pattarong-RAE/Cheetah_Cube_Inspire/Model/bio/oox foot.SLDPRT

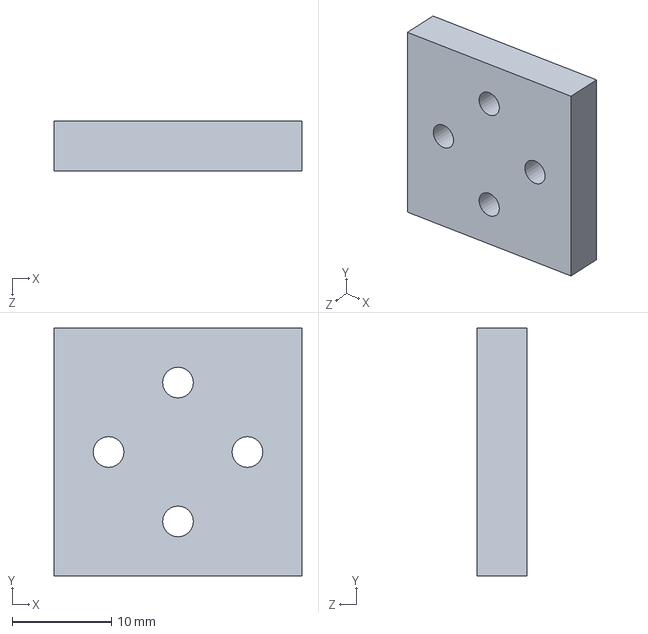
[picture p48: CAD file, 2023-05-24]
Model/bio/oox foot.SLDPRT
25.0 x 25.0 x 5.00 mm
