pattarong-RAE/Cheetah_Cube_Inspire/Model/bio/foot and body/footRingPlate.SLDPRT

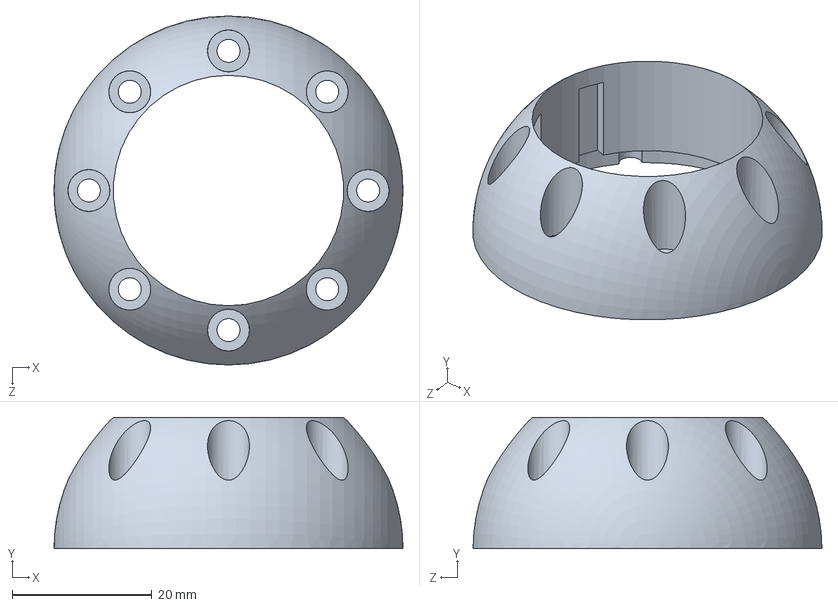
[picture p49: CAD file, 2023-05-24]
Model/bio/foot and body/footRingPlate.SLDPRT
50.0 x 18.8 x 50.0 mm
