pattarong-RAE/Cheetah_Cube_Inspire/Model/bio/sevo smail 2.SLDPRT

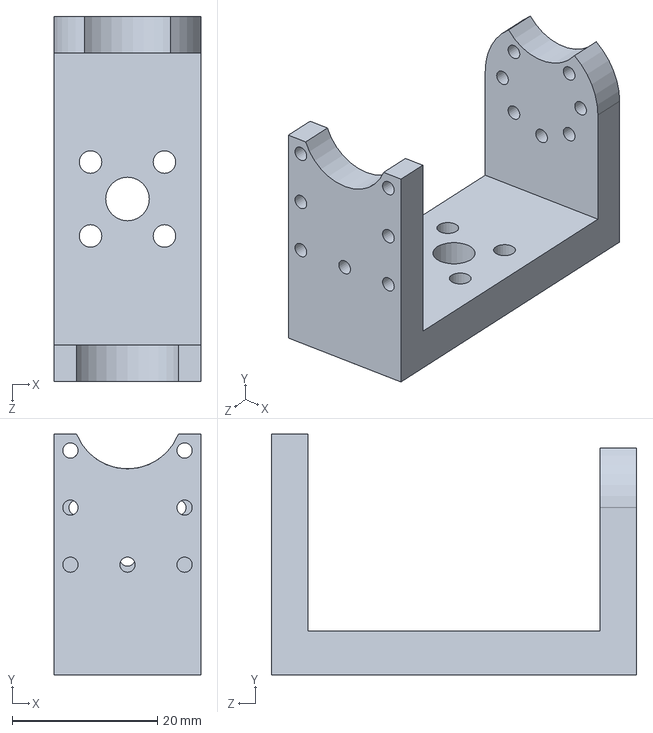
[picture p50: CAD file, 2023-05-24]
Model/bio/sevo smail 2.SLDPRT
20.2 x 33.1 x 50.2 mm
