pattarong-RAE/Cheetah_Cube_Inspire/Model/bio/foot and body/footButtonPlate.SLDPRT

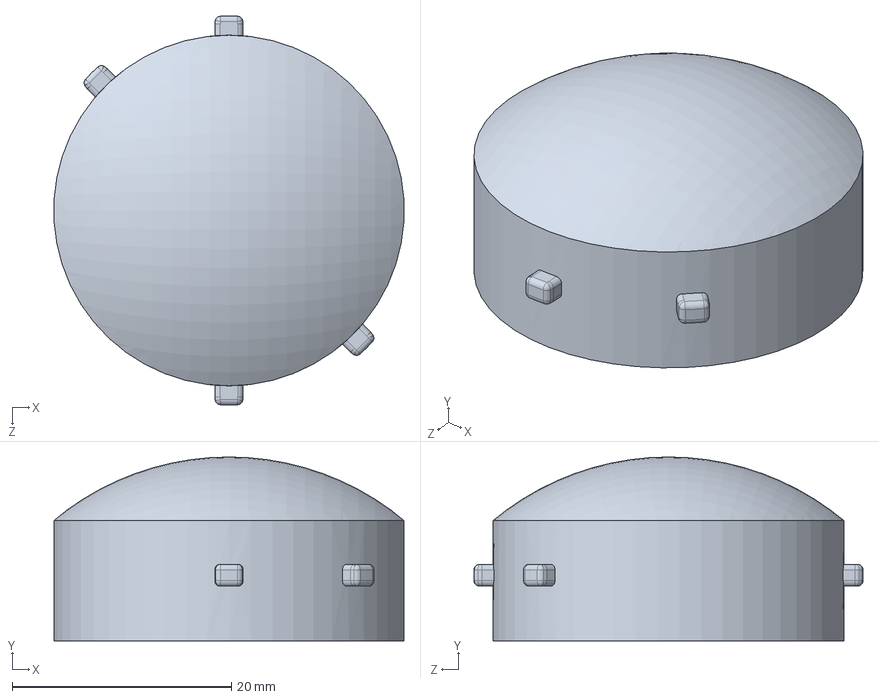
[picture p51: CAD file, 2023-05-24]
Model/bio/foot and body/footButtonPlate.SLDPRT
31.9 x 16.8 x 35.5 mm
