pattarong-RAE/Cheetah_Cube_Inspire/Model/bio/oox leg.SLDPRT

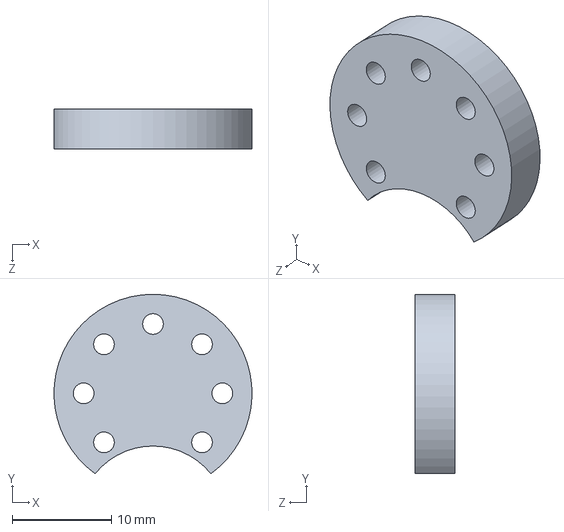
[picture p52: CAD file, 2023-05-24]
Model/bio/oox leg.SLDPRT
20.0 x 18.1 x 4.00 mm
