pattarong-RAE/Cheetah_Cube_Inspire/Model/bio/foot and body/midFootSLDPRT.sldprt

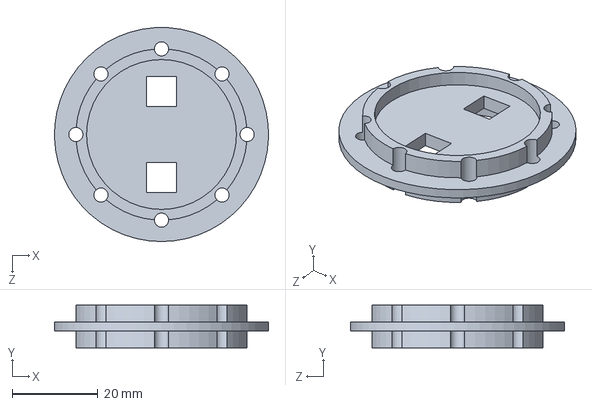
[picture p53: CAD file, 2023-05-24]
Model/bio/foot and body/midFootSLDPRT.sldprt
50.0 x 10.0 x 50.0 mm
