pattarong-RAE/Cheetah_Cube_Inspire/Model/bio/servo long.SLDPRT

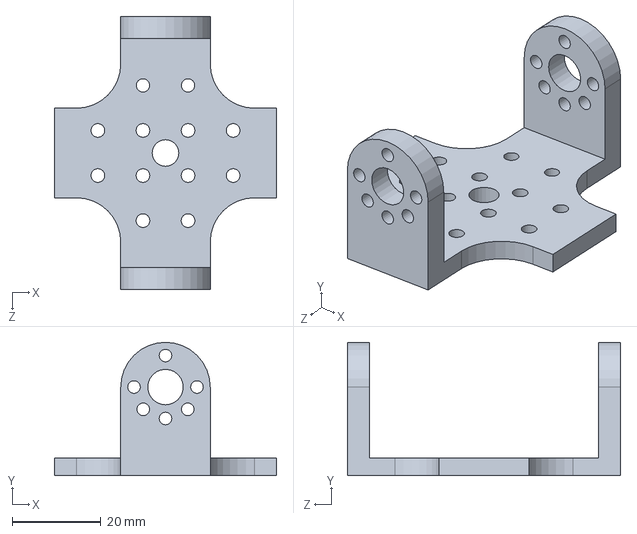
[picture p54: CAD file, 2023-05-24]
Model/bio/servo long.SLDPRT
50.2 x 30.1 x 61.6 mm
