pattarong-RAE/Cheetah_Cube_Inspire/Model/bio/foot and body/Support_Foot_con.SLDPRT

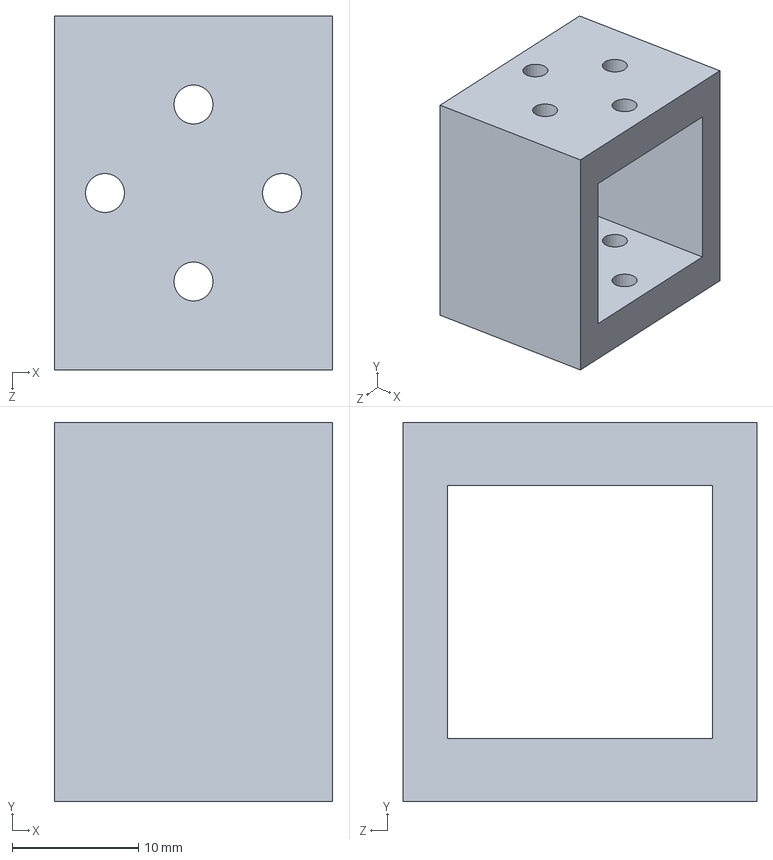
[picture p55: CAD file, 2023-05-24]
Model/bio/foot and body/Support_Foot_con.SLDPRT
22.0 x 30.0 x 28.0 mm
