pattarong-RAE/Cheetah_Cube_Inspire/Model/bio/foot and body/Part1.SLDPRT

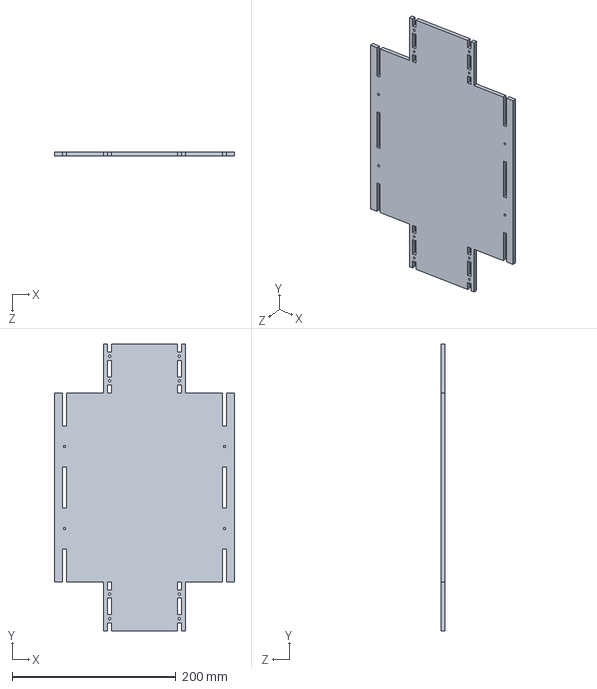
[picture p56: CAD file, 2023-05-24]
Model/bio/foot and body/Part1.SLDPRT
220.0 x 350.0 x 5.00 mm
