pattarong-RAE/Cheetah_Cube_Inspire/Model/bio/servo.SLDPRT

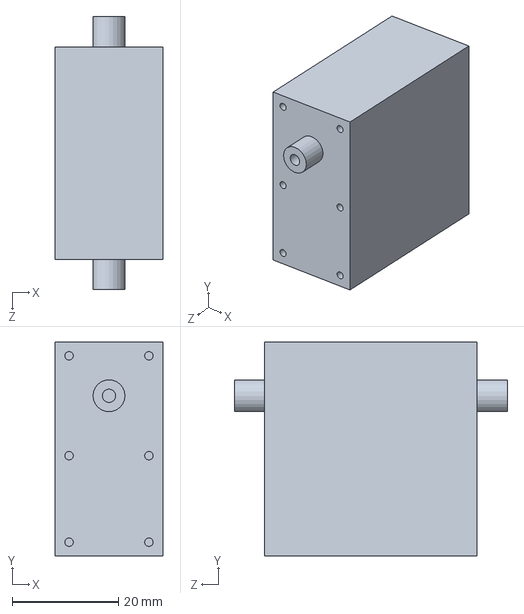
[picture p57: CAD file, 2023-05-24]
Model/bio/servo.SLDPRT
20.2 x 40.2 x 51.3 mm
