pattarong-RAE/Cheetah_Cube_Inspire/Model/bio/sevo smail.SLDPRT

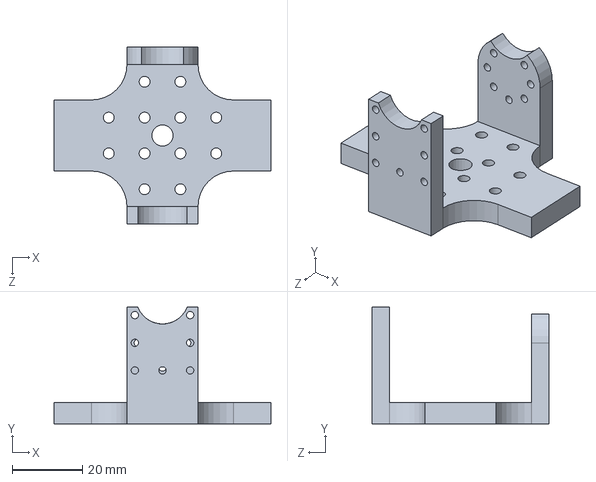
[picture p58: CAD file, 2023-05-24]
Model/bio/sevo smail.SLDPRT
61.6 x 33.1 x 50.2 mm
