pattarong-RAE/Cheetah_Cube_Inspire/Model/bio/oox leg right_edit.SLDPRT

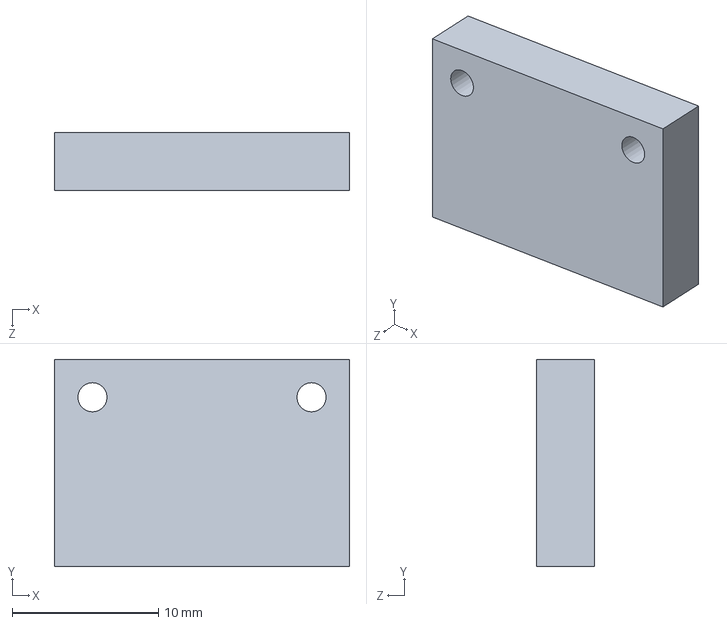
[picture p59: CAD file, 2023-05-24]
Model/bio/oox leg right_edit.SLDPRT
20.2 x 14.2 x 4.00 mm
